jalhuneidi1/ECE411_F2021_Team11/Hardware/sunrise-alarm/sunrise-alarm.kicad_pcb

## KiCad design design/electrical/communication_system.sch

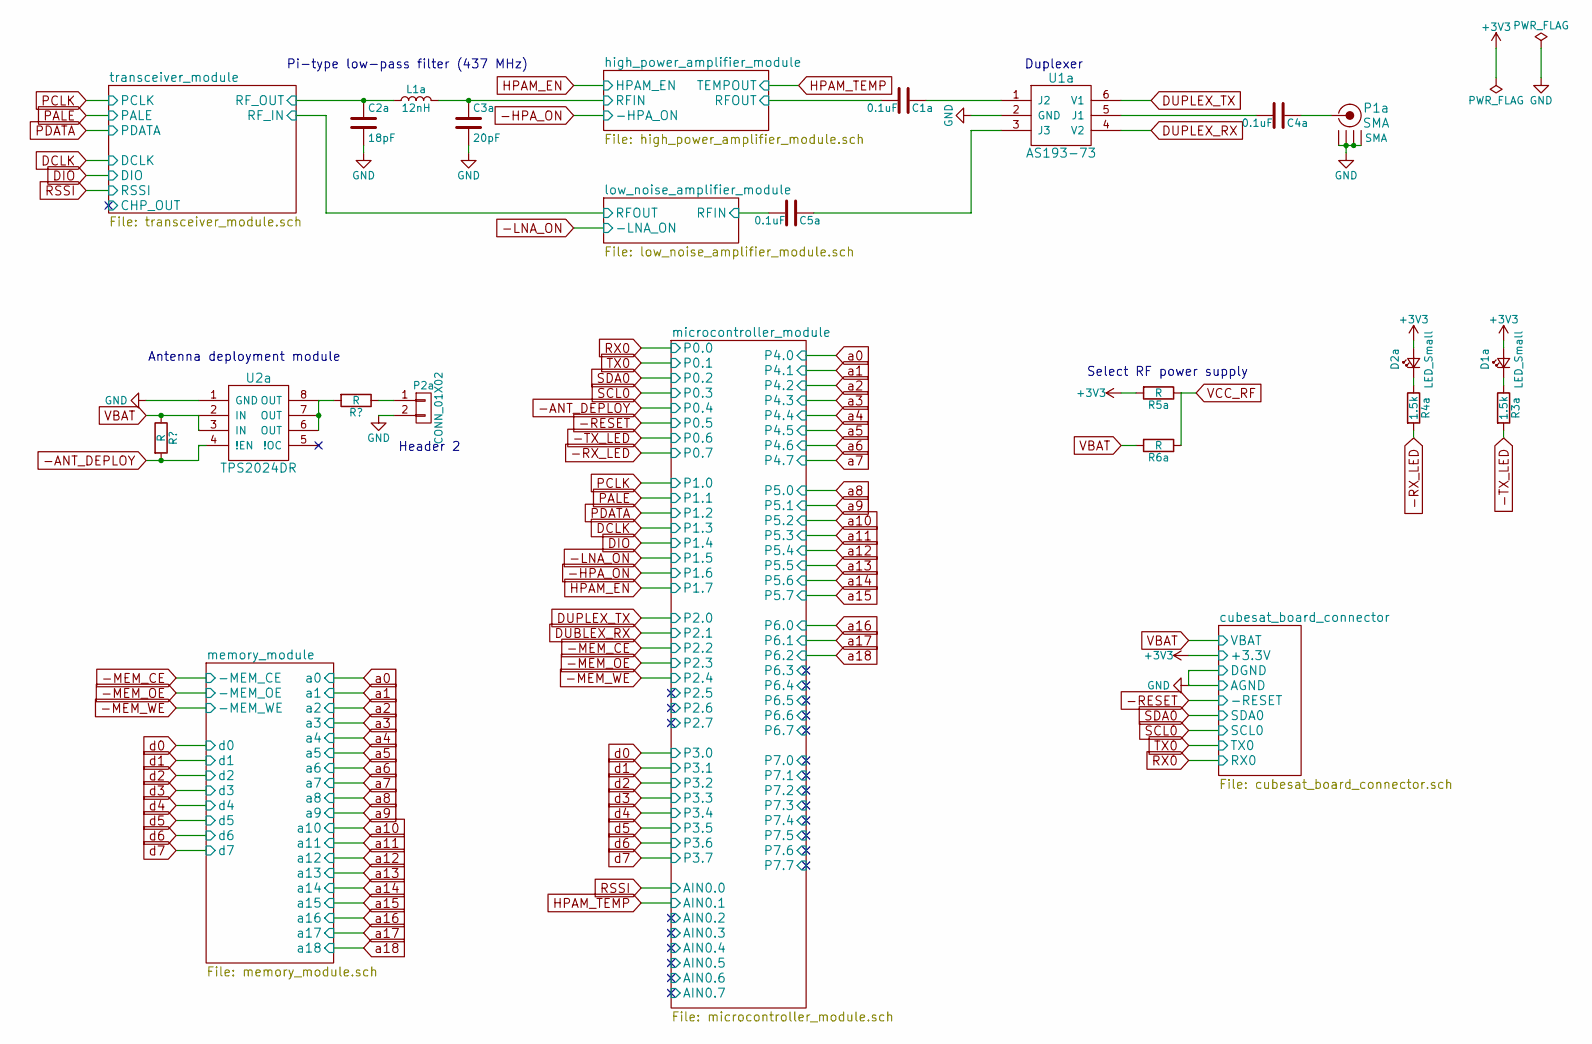
[picture p7: schematic communication_system.sch]

Parts:
12nH: L1a
C1a, C4a, C5a: 0.1uF
C2a: 18pF
C3a: 20pF
D1a, D2a: LED_Small
P1a: SMA
P2a: CONN_01X02
R3a, R4a: 1.5k
R5a, R6a: R
U1a: AS193-73
U2a: TPS2024DR

Connections:
+3V3: D1a.2 (A), D2a.2 (A), R5a.2
-ANT_DEPLOY: U2a.4 (!EN)
-RX_LED: R4a.2
-TX_LED: R3a.2
DUPLEX_RX: U1a.4 (V2)
DUPLEX_TX: U1a.6 (V1)
GND: C2a.2, C3a.2, P1a.2 (GND1), P1a.3 (GND2), P1a.4 (GND3), P1a.5 (GND4), P2a.2, U1a.2 (GND), U2a.1 (GND)
unnamed: C1a.1, U1a.1 (J2)
unnamed: C4a.1, P1a.1 (RF)
unnamed: C4a.2, U1a.5 (J1)
unnamed: C5a.1, U1a.3 (J3)
unnamed: D1a.1 (K), R3a.1
unnamed: D2a.1 (K), R4a.1
unnamed: U2a.6 (OUT), U2a.7 (OUT), U2a.8 (OUT)
RFIN: 12nH.2, C3a.1, C5a.2
RFOUT: C1a.2
RF_OUT: 12nH.1, C2a.1
VBAT: R6a.2, U2a.2 (IN), U2a.3 (IN)
VCC_RF: R5a.1, R6a.1

Notes on the sheet:
Header 2
Antenna deployment module
Pi-type low-pass filter (437 MHz)
Duplexer
Select RF power supply
